SeamusIngram/rana-tadpole-with-legs/Modified Files/V3/motherboard v3/outline.dxf

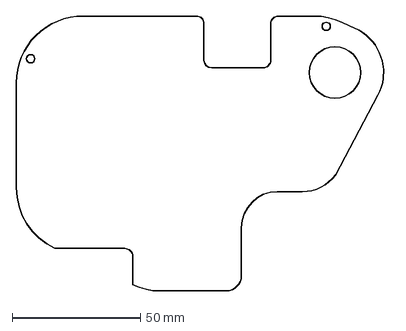
[picture p15: CAD file, 2023-12-28]
Modified Files/V3/motherboard v3/outline.dxf
145.3 x 107.0 mm
