SeamusIngram/rana-tadpole-with-legs/Modified Files/V3/Separate Grip CAD/grip.step

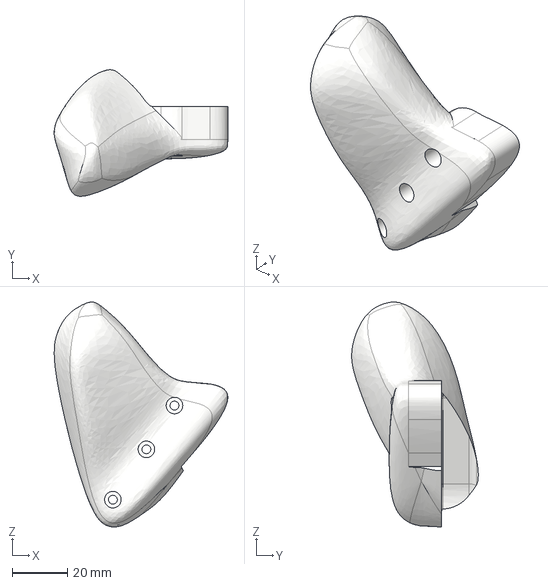
[picture p16: CAD file, 2023-12-28]
Modified Files/V3/Separate Grip CAD/grip.step
62.9 x 45.8 x 81.4 mm
