SeamusIngram/rana-tadpole-with-legs/Modified Files/CAD - Same between versions/Pushbutton.step

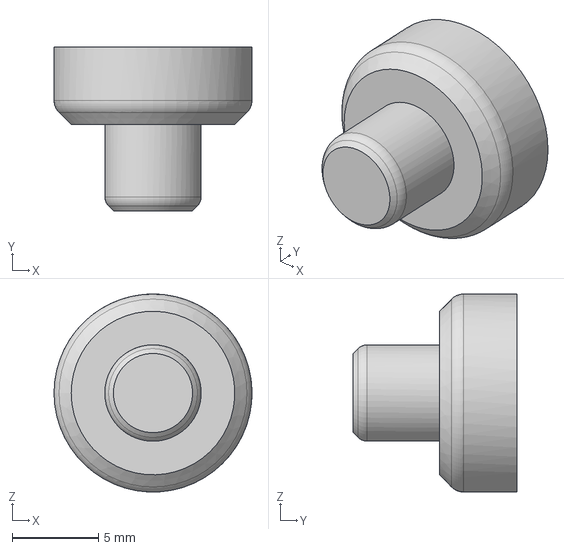
[picture p17: CAD file, 2023-11-24]
Modified Files/CAD - Same between versions/Pushbutton.step
11.5 x 9.50 x 11.5 mm
