SeamusIngram/rana-tadpole-with-legs/Modified Files/V1 - Don't make this/CAD/magnet_gate_4_0-6_tolerance.step

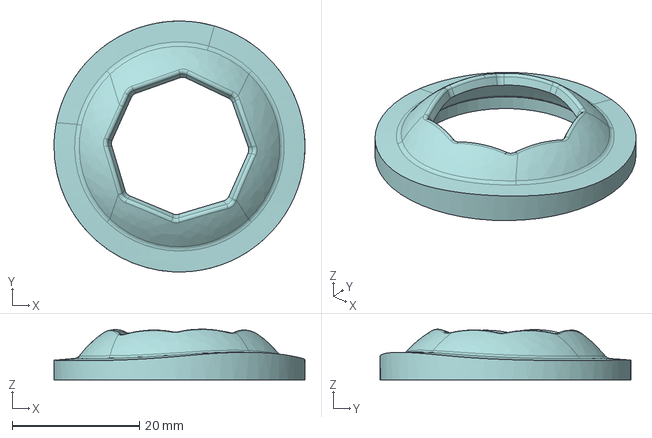
[picture p18: CAD file, 2023-11-24]
Modified Files/V1 - Don't make this/CAD/magnet_gate_4_0-6_tolerance.step
39.4 x 39.4 x 7.95 mm
