SeamusIngram/rana-tadpole-with-legs/Modified Files/V1 - Don't make this/Mainboard-small-buttons/OlyU-big.dxf

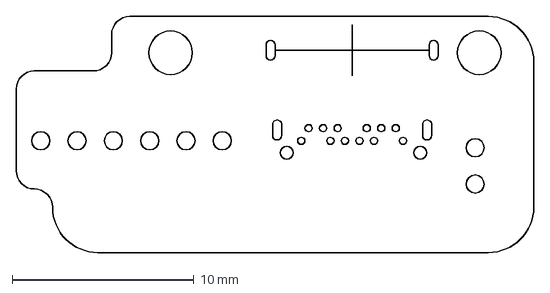
[picture p19: CAD file, 2023-10-06]
Modified Files/V1 - Don't make this/Mainboard-small-buttons/OlyU-big.dxf
28.5 x 13.0 mm
