SeamusIngram/rana-tadpole-with-legs/Modified Files/V3/CAD/notched gate.step

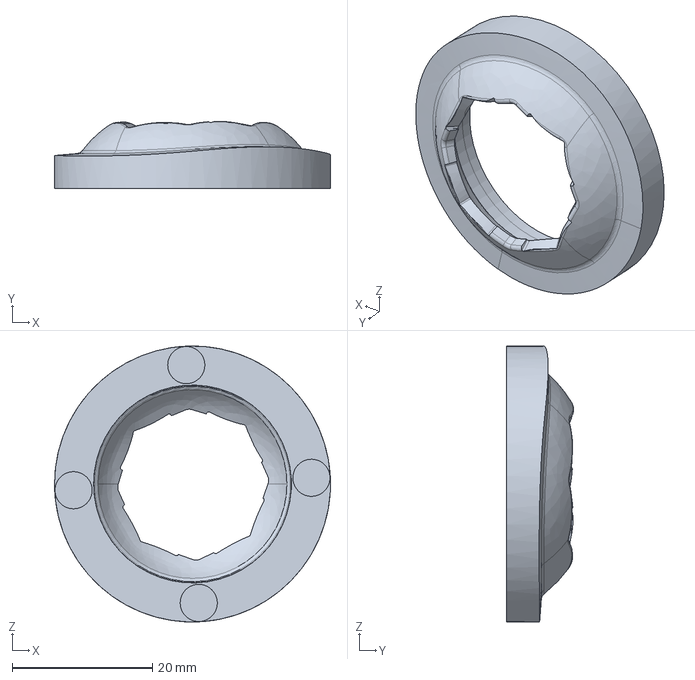
[picture p20: CAD file, 2023-12-28]
Modified Files/V3/CAD/notched gate.step
39.4 x 9.61 x 39.4 mm
