SeamusIngram/rana-tadpole-with-legs/Modified Files/V3/motherboard v3/outline trigger.dxf

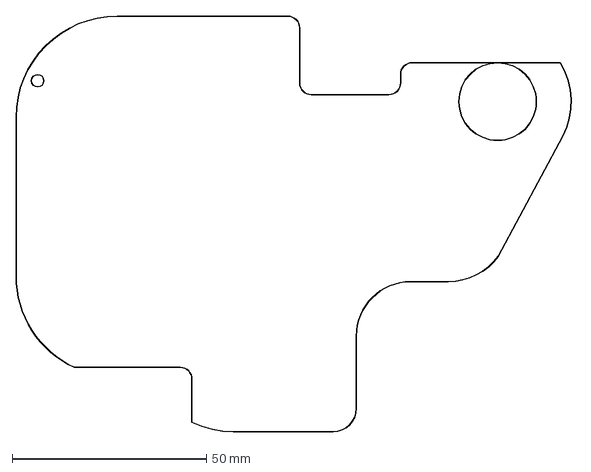
[picture p21: CAD file, 2023-12-28]
Modified Files/V3/motherboard v3/outline trigger.dxf
143.9 x 107.0 mm
