SeamusIngram/rana-tadpole-with-legs/Modified Files/V3/Separate Grip CAD/case.step

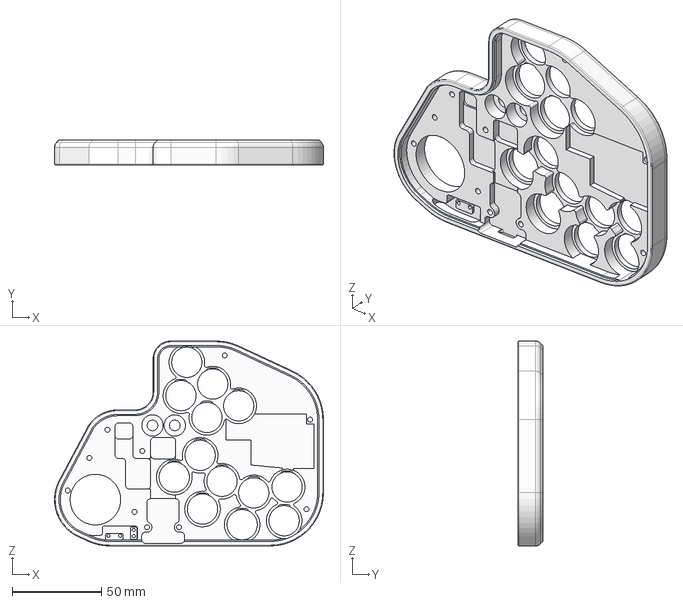
[picture p22: CAD file, 2023-12-28]
Modified Files/V3/Separate Grip CAD/case.step
150.9 x 14.0 x 115.0 mm
