SeamusIngram/rana-tadpole-with-legs/Modified Files/CAD - Same between versions/GCC Handle.step

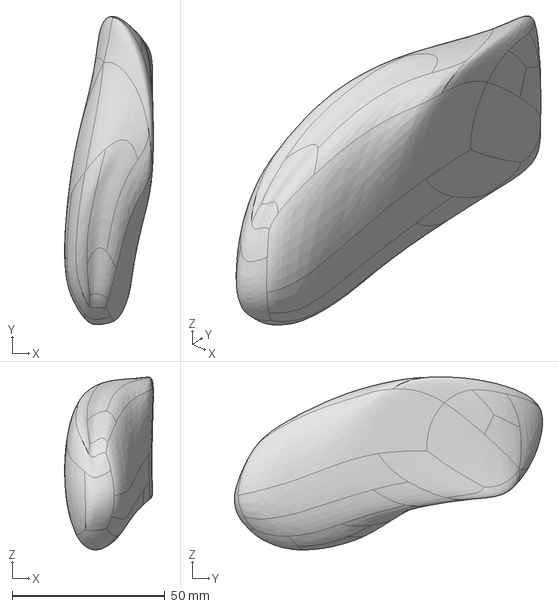
[picture p23: CAD file, 2023-10-06]
Modified Files/CAD - Same between versions/GCC Handle.step
29.0 x 100.7 x 56.5 mm
