SeamusIngram/rana-tadpole-with-legs/Modified Files/V1 - Don't make this/CAD/trigger_v1.step

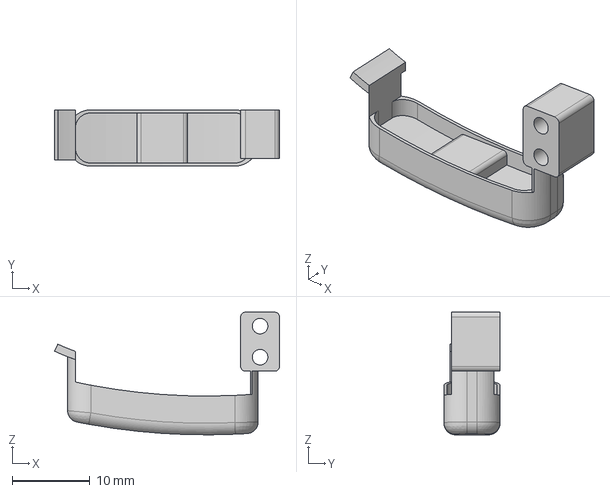
[picture p24: CAD file, 2023-11-24]
Modified Files/V1 - Don't make this/CAD/trigger_v1.step
29.0 x 7.25 x 15.8 mm
Case
Trigger
