SeamusIngram/rana-tadpole-with-legs/Modified Files/V3/CAD/stand.step

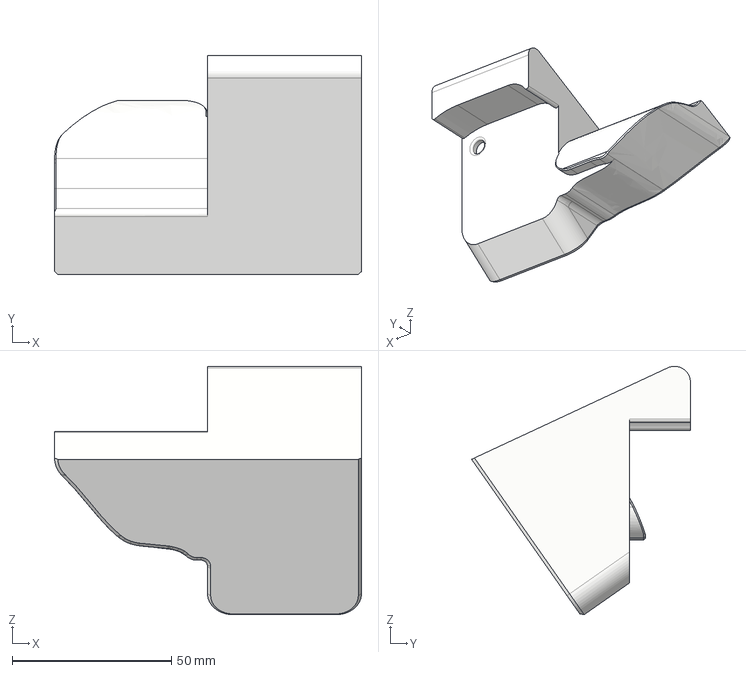
[picture p25: CAD file, 2023-12-28]
Modified Files/V3/CAD/stand.step
96.5 x 68.8 x 78.0 mm
Case
Stand
