SeamusIngram/rana-tadpole-with-legs/Modified Files/V3/motherboard v3/slots.step

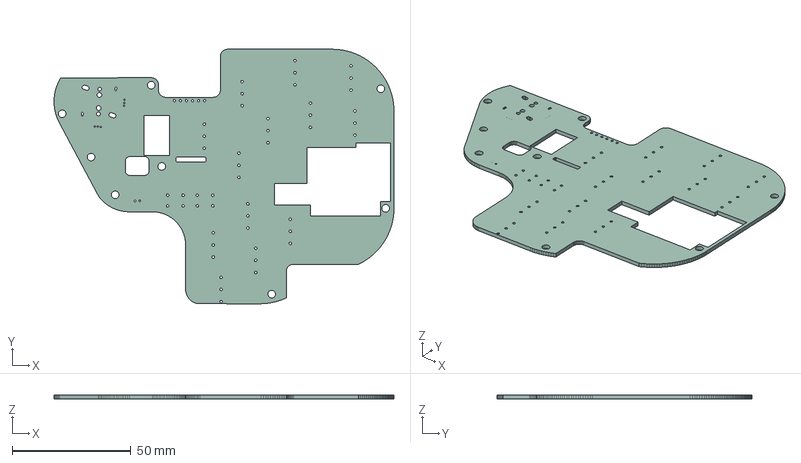
[picture p26: CAD file, 2023-12-28]
Modified Files/V3/motherboard v3/slots.step
142.9 x 107.0 x 1.58 mm
