SeamusIngram/rana-tadpole-with-legs/Modified Files/CAD - Same between versions/Xbox Handle.step

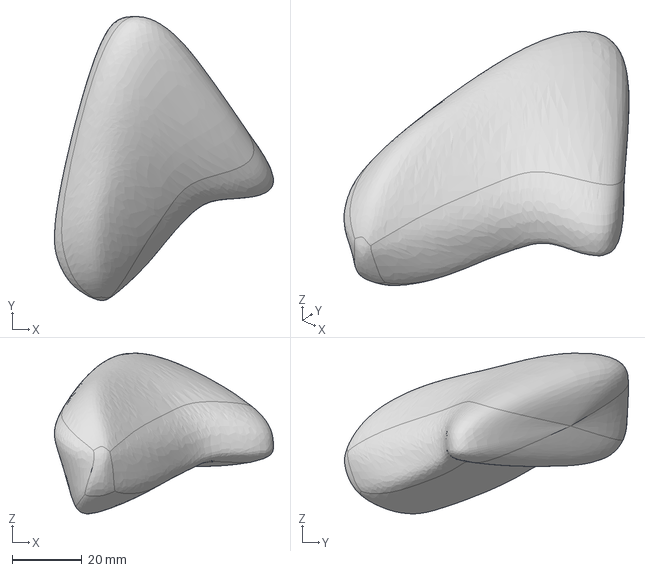
[picture p27: CAD file, 2023-10-06]
Modified Files/CAD - Same between versions/Xbox Handle.step
62.9 x 81.5 x 46.1 mm
