SeamusIngram/rana-tadpole-with-legs/Modified Files/V1 - Don't make this/CAD/case_v1.step

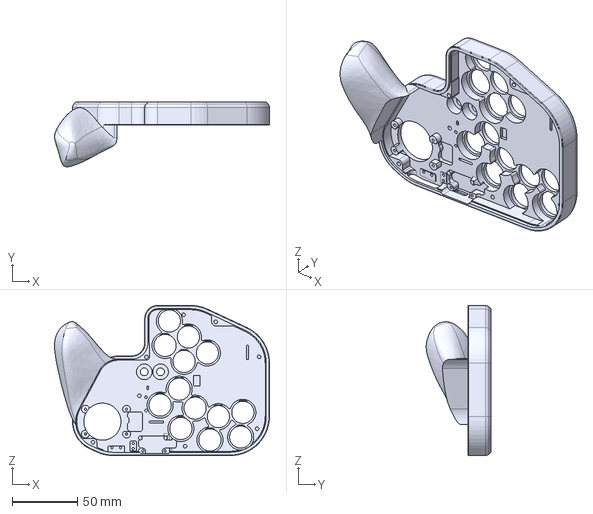
[picture p28: CAD file, 2023-11-24]
Modified Files/V1 - Don't make this/CAD/case_v1.step
164.7 x 49.6 x 115.0 mm
