SeamusIngram/rana-tadpole-with-legs/Modified Files/V3/CAD/trigger.step

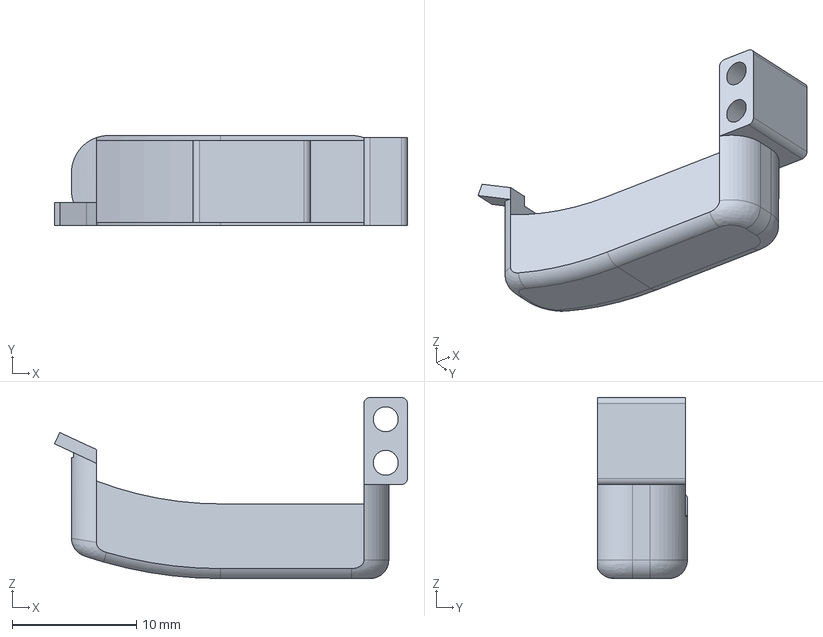
[picture p29: CAD file, 2023-12-28]
Modified Files/V3/CAD/trigger.step
28.4 x 7.23 x 14.6 mm
