SeamusIngram/rana-tadpole-with-legs/Modified Files/V3/motherboard v3/Rana Tadpole PCB.step

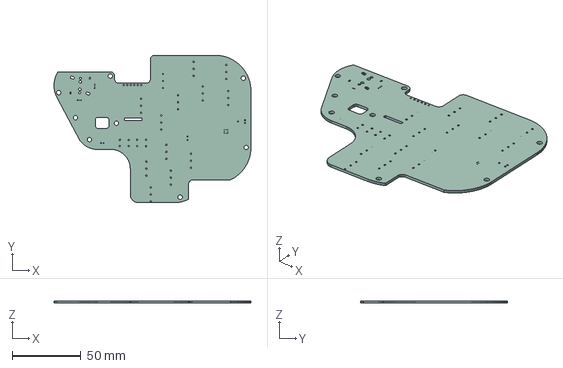
[picture p30: CAD file, 2023-12-28]
Modified Files/V3/motherboard v3/Rana Tadpole PCB.step
142.9 x 107.0 x 1.58 mm
